Pier1965/MonCafeRadio/Docs/Bom/img/Condensatori.png

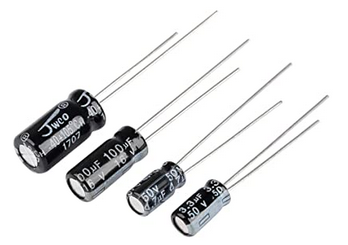
Docs/Bom/img/Condensatori.png
