Pier1965/MonCafeRadio/Docs/Bom/img/IR.png

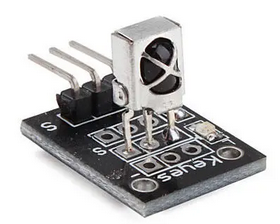
Docs/Bom/img/IR.png
