Pier1965/MonCafeRadio/Docs/Bom/img/OLED-1603.png

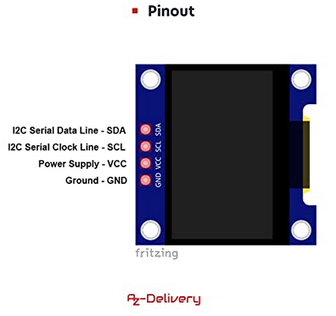
Docs/Bom/img/OLED-1603.png
