Pier1965/MonCafeRadio/Docs/Bom/img/presa-55.png

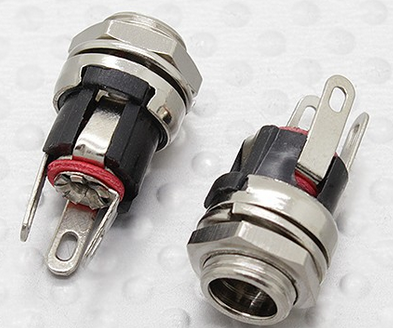
Docs/Bom/img/presa-55.png
