Pier1965/MonCafeRadio/Docs/Bom/img/Pulsanti.png

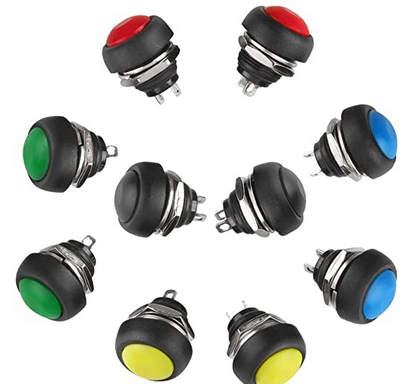
Docs/Bom/img/Pulsanti.png
