Pier1965/MonCafeRadio/Docs/Bom/img/Radio.jpg

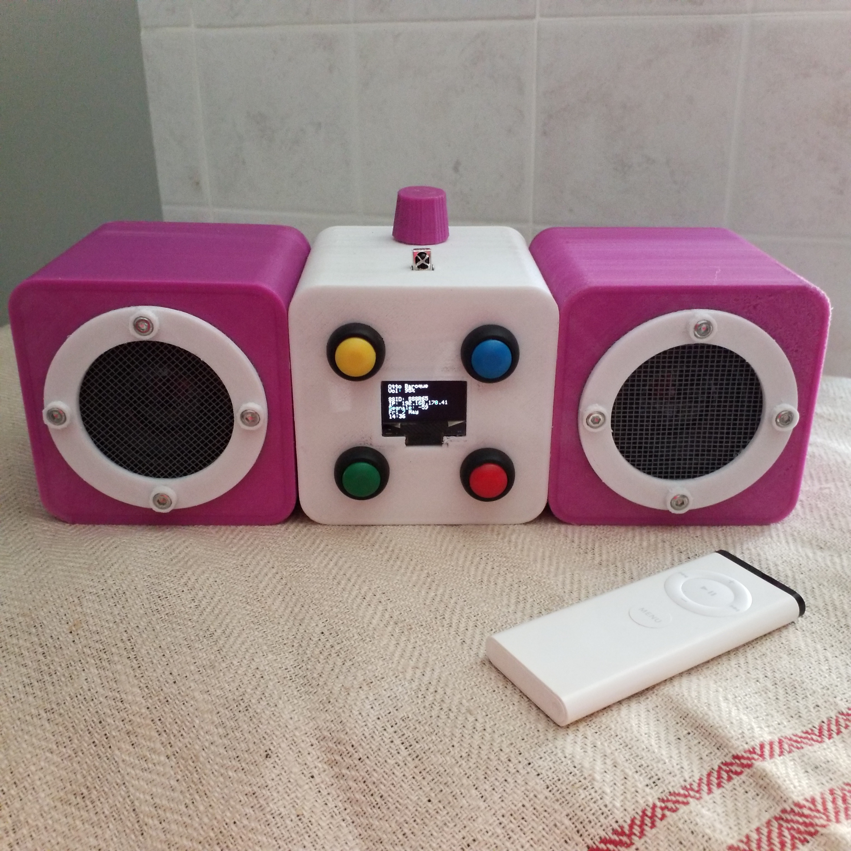
Docs/Bom/img/Radio.jpg
