Pier1965/MonCafeRadio/Docs/Bom/img/Resistenza.png

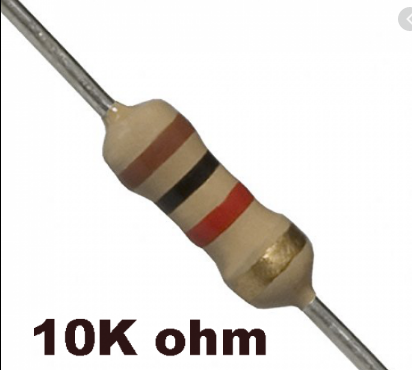
Docs/Bom/img/Resistenza.png
