Pier1965/MonCafeRadio/Docs/Bom/img/speakers.png

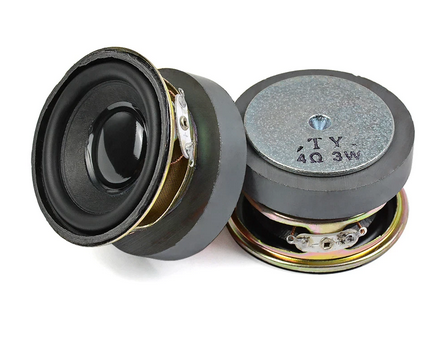
Docs/Bom/img/speakers.png
