Pier1965/MonCafeRadio/Docs/Bom/img/T1-1-600-600.png

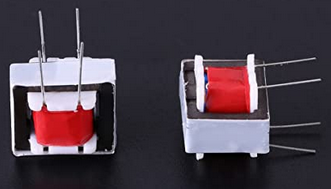
Docs/Bom/img/T1-1-600-600.png
