Pier1965/MonCafeRadio/Docs/Bom/img/VS1053.png

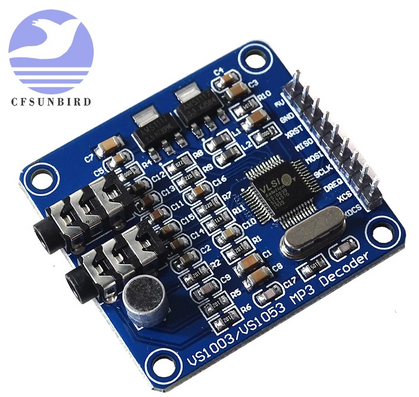
Docs/Bom/img/VS1053.png
